rckTom/fusion-egg/media/grafiken/cad/zusammenbau1.PNG

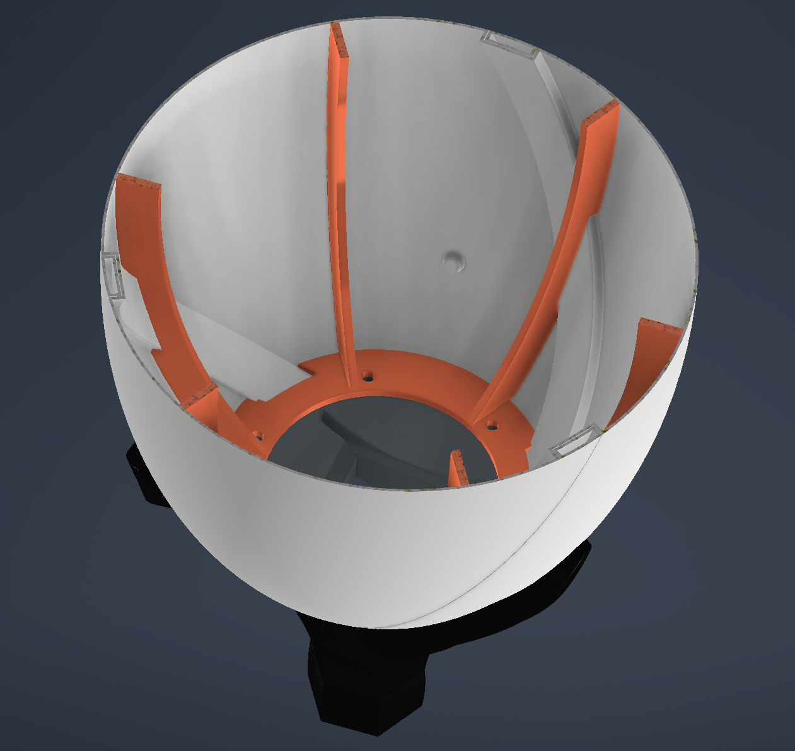
media/grafiken/cad/zusammenbau1.PNG
