rckTom/fusion-egg/media/grafiken/fusion_bilder/6.jpg

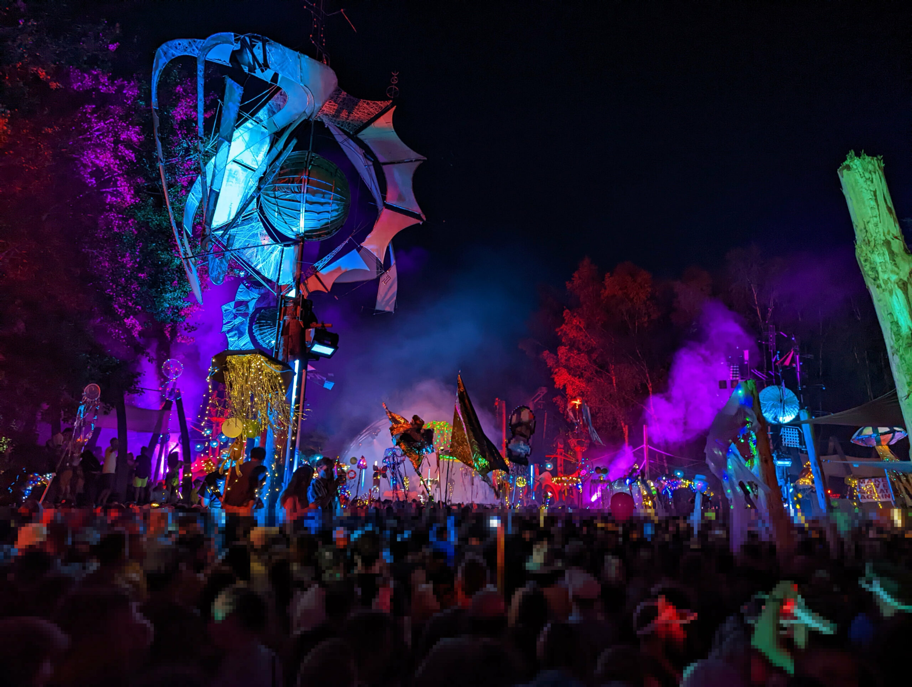
media/grafiken/fusion_bilder/6.jpg
