rckTom/fusion-egg/media/grafiken/illustrationen/vase_sliced.PNG

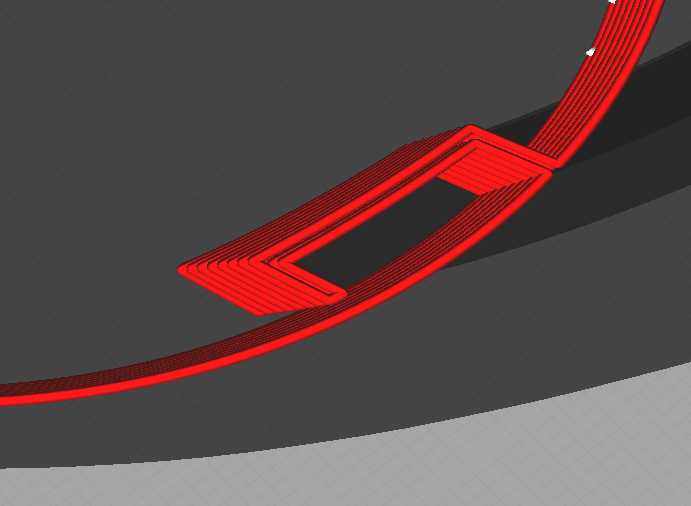
media/grafiken/illustrationen/vase_sliced.PNG
