rckTom/fusion-egg/media/grafiken/kitchen_bilder/DSC07974.JPG

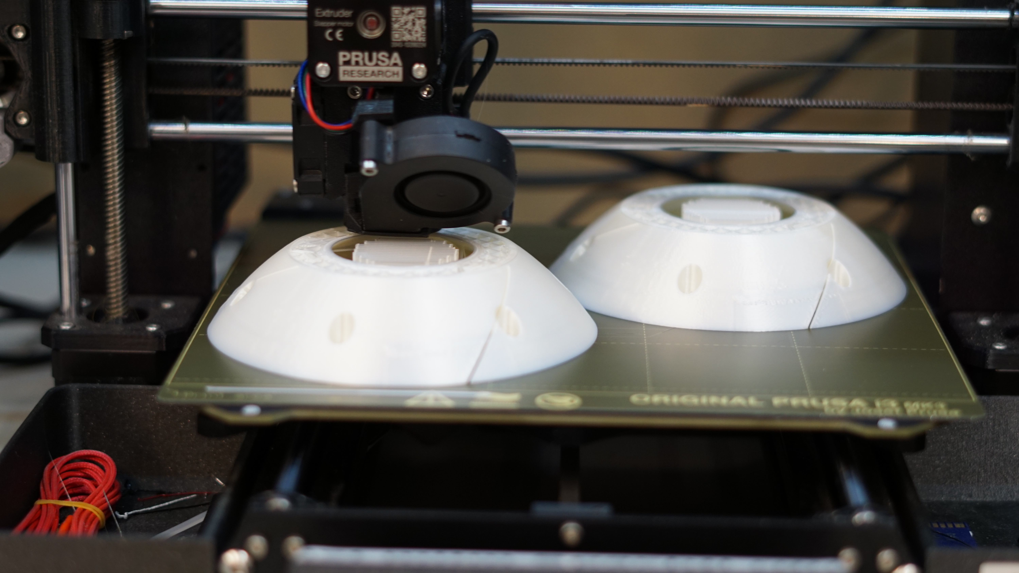
media/grafiken/kitchen_bilder/DSC07974.JPG
