rckTom/fusion-egg/media/grafiken/kitchen_bilder/DSC07983.JPG

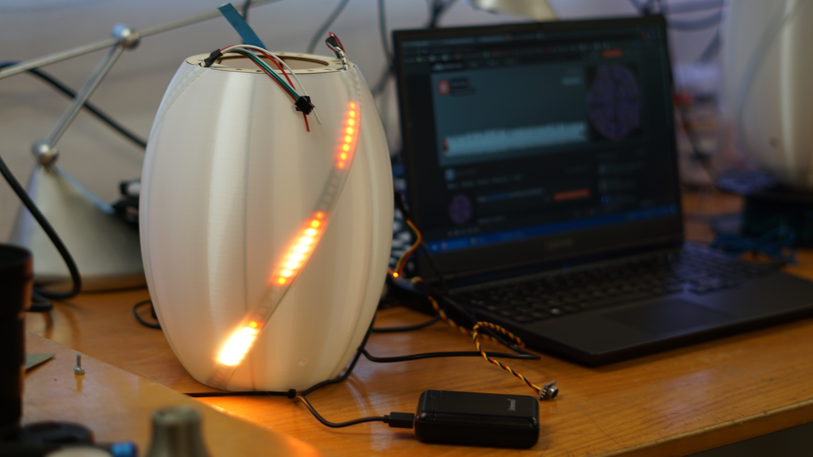
media/grafiken/kitchen_bilder/DSC07983.JPG
