rckTom/fusion-egg/cad_3stripes/boden.stl

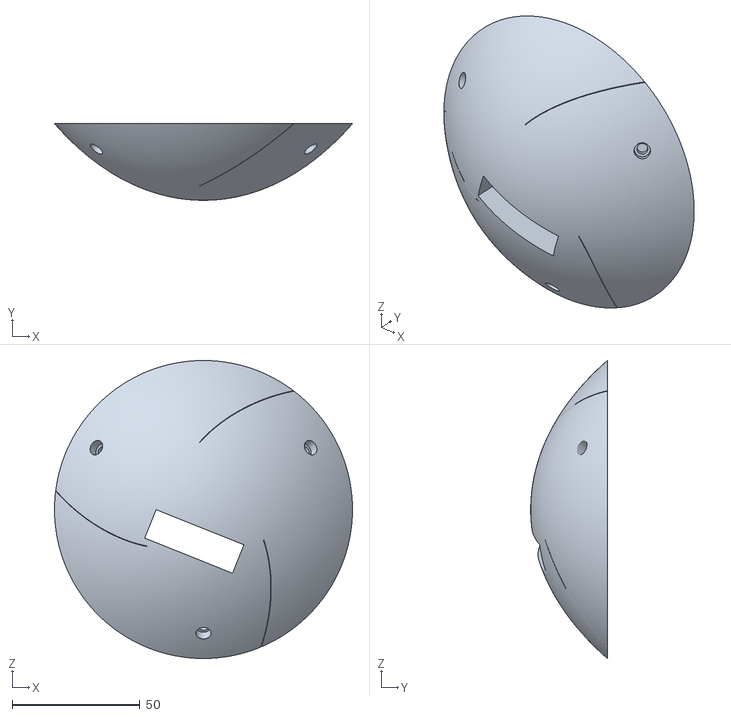
[picture p28: CAD file, 2022-06-24]
cad_3stripes/boden.stl
116.6 x 30.0 x 116.6
