rckTom/fusion-egg/cad_3stripes/aussenhaut.stp

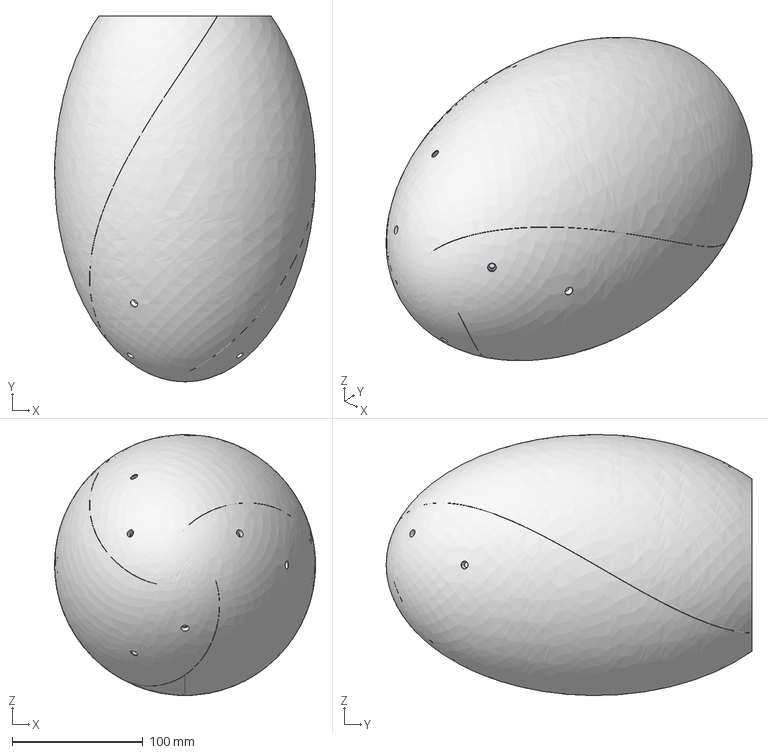
[picture p29: CAD file, 2022-06-19]
cad_3stripes/aussenhaut.stp
199.9 x 280.0 x 200.0 mm
