rckTom/fusion-egg/media/grafiken/kitchen_bilder/DSC07971.JPG

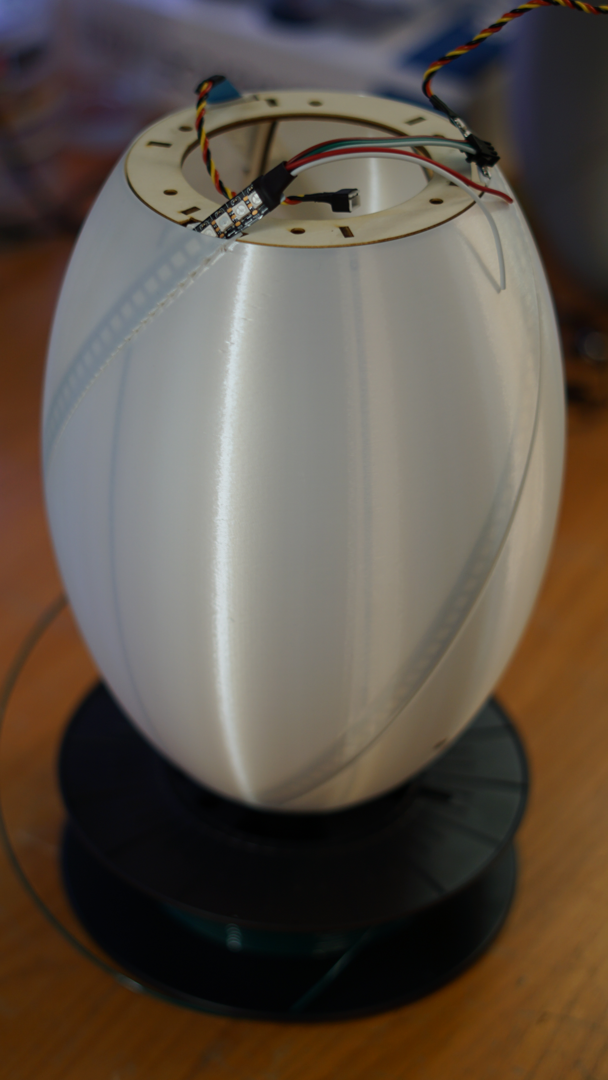
media/grafiken/kitchen_bilder/DSC07971.JPG
